barack-hash/offline-survival-llm/scripts/eval_models.py

"""
eval_models.py — head-to-head model comparison on the device.

Runs the Phase 4 battery (eval_questions.QUESTIONS) plus extra refusal and
dosage cases through the exact device pipeline (same retrieval, prompts,
temperatures, context size) for one model, and records per question:
time to first token, generation tokens/sec, token counts, and the answer.
Peak RAM of the whole process is reported at the end.

Run from the project root, one model at a time (stop survival-llm first so
two models aren't loaded at once):

    PYTHONPATH=scripts venv/bin/python scripts/eval_models.py models/<file>.gguf

Results are appended as JSON lines to eval_results/<model>.jsonl.
"""

import json
import os
import resource
import sys
import time

from llama_cpp import Llama
from sentence_transformers import SentenceTransformer

from eval_questions import QUESTIONS
from main import (
    load_index, retrieve, build_messages, is_critical,
    TOP_K, CRITICAL_TOP_K,
)

# Extra cases aimed at the two behaviours that matter most for safety:
# refusing when the library doesn't cover it, and quoting doses exactly.
EXTRA = [
    ("out_of_corpus", "What is the current price of gold per ounce?"),
    ("out_of_corpus", "How do I reset the password on my wifi router?"),
    ("critical",      "What is the dose of acetaminophen for a child 8 to 12 years old?"),
]


def peak_rss_mb():
    return resource.getrusage(resource.RUSAGE_SELF).ru_maxrss / 1024


def main(model_path):
    name = os.path.basename(model_path).replace(".gguf", "")
    os.makedirs("eval_results", exist_ok=True)
    out_path = f"eval_results/{name}.jsonl"

    embedder = SentenceTransformer("all-MiniLM-L6-v2")
    index, chunks = load_index()
    rss_before_llm = peak_rss_mb()
    t0 = time.time()
    llm = Llama(model_path=model_path, n_ctx=4096, n_threads=4, verbose=False)
    load_s = time.time() - t0
    rss_after_load = peak_rss_mb()
    print(f"MODEL {name}  load {load_s:.1f}s  RSS before LLM {rss_before_llm:.0f} MB, after load {rss_after_load:.0f} MB",
          flush=True)

    with open(out_path, "w") as out:
        for i, (category, question) in enumerate(QUESTIONS + EXTRA, 1):
            critical = is_critical(question)
            retrieved = retrieve(question, embedder, index, chunks,
                                 k=CRITICAL_TOP_K if critical else TOP_K)
            messages = build_messages(question, retrieved, critical=critical)

            start = time.time()
            first = None
            text = ""
            n_tokens = 0
            for chunk in llm.create_chat_completion(
                    messages=messages, max_tokens=400,
                    temperature=0.0 if critical else 0.3, stream=True):
                delta = chunk["choices"][0]["delta"].get("content")
                if delta:
                    if first is None:
                        first = time.time()
                    text += delta
                    n_tokens += 1
            end = time.time()
            prompt_tokens = len(llm.tokenize(json.dumps(messages).encode()))   # approximate
            gen_s = (end - first) if first else 0.0
            rec = {
                "model": name, "n": i, "category": category, "critical_mode": critical,
                "question": question,
                "sources": sorted({r["source"] for r in retrieved}),
                "ttft_s": round((first or end) - start, 1),
                "gen_tokens": n_tokens,
                "gen_tps": round(n_tokens / gen_s, 2) if gen_s > 0 else None,
                "prompt_tokens_approx": prompt_tokens,
                "answer": text.strip(),
            }
            out.write(json.dumps(rec) + "\n")
            out.flush()
            print(f"[{i}/{len(QUESTIONS) + len(EXTRA)}] {category:13s} ttft {rec['ttft_s']:5.1f}s  "
                  f"gen {rec['gen_tps']} tok/s  {n_tokens} tok  | {question[:50]}", flush=True)

    print(f"DONE {name}  peak RSS {peak_rss_mb():.0f} MB  (LLM share ≈ {peak_rss_mb() - rss_before_llm:.0f} MB)",
          flush=True)


if __name__ == "__main__":
    main(sys.argv[1])
